Webring/ASTRI/Mechanical/front side of table.SLDPRT

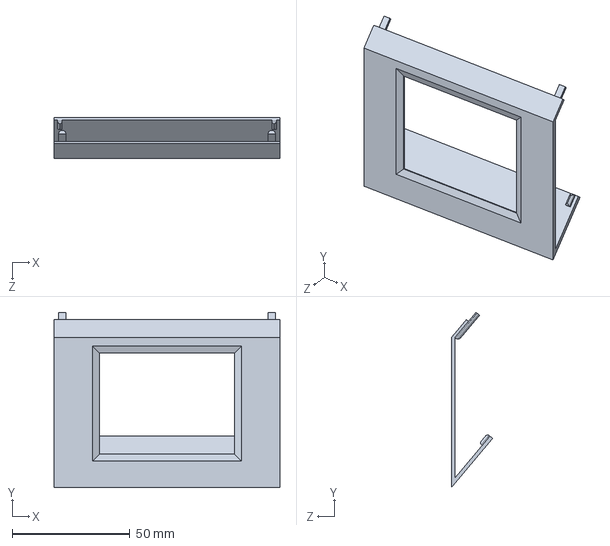
[picture p17: CAD file, 2019-09-15]
Mechanical/front side of table.SLDPRT
96.0 x 74.5 x 17.6 mm
