Webring/ASTRI/Mechanical/table bottom.SLDPRT

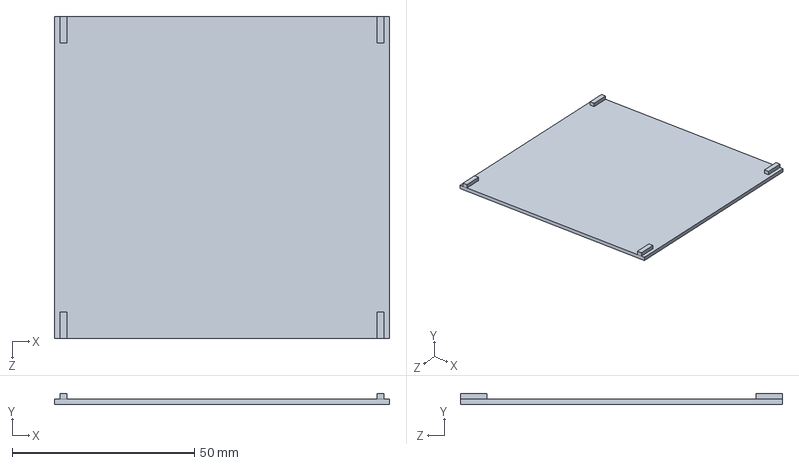
[picture p18: CAD file, 2019-09-15]
Mechanical/table bottom.SLDPRT
92.0 x 3.00 x 88.5 mm
