Webring/ASTRI/Mechanical/switch nozzle.SLDPRT

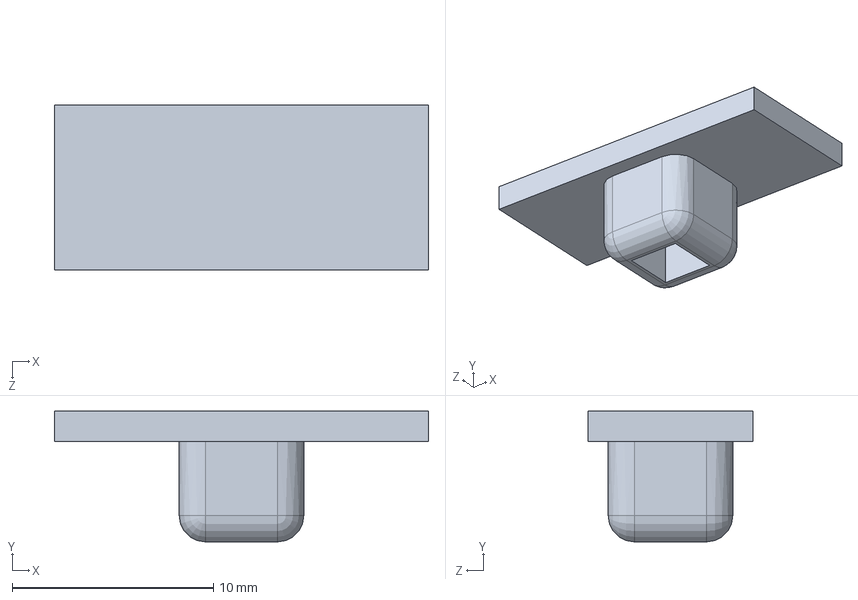
[picture p19: CAD file, 2019-09-15]
Mechanical/switch nozzle.SLDPRT
18.6 x 6.50 x 8.20 mm
