Webring/ASTRI/Mechanical/drum head.SLDPRT

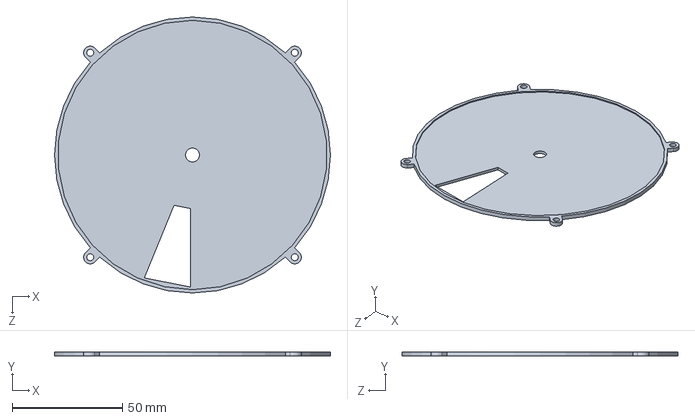
[picture p20: CAD file, 2019-08-11]
Mechanical/drum head.SLDPRT
125.0 x 2.00 x 125.0 mm
