Webring/ASTRI/Mechanical/drum body.SLDPRT

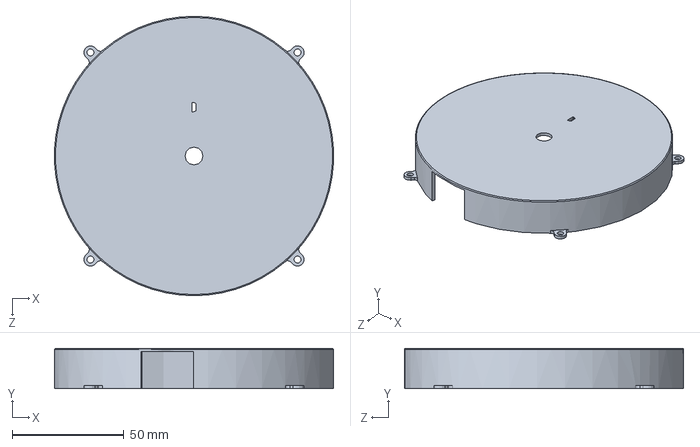
[picture p21: CAD file, 2019-08-11]
Mechanical/drum body.SLDPRT
124.8 x 18.0 x 125.0 mm
