Webring/ASTRI/Mechanical/motor mount to drum.SLDPRT

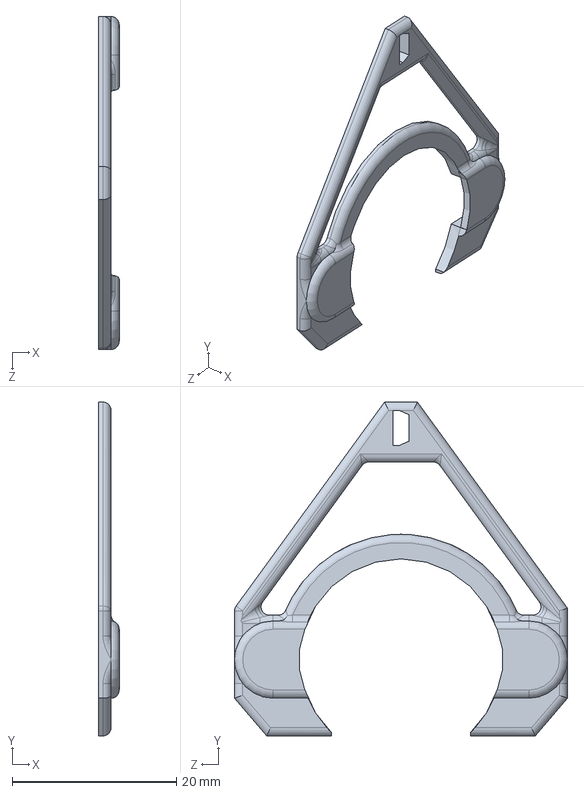
[picture p22: CAD file, 2019-08-11]
Mechanical/motor mount to drum.SLDPRT
2.50 x 40.6 x 40.5 mm
