Webring/ASTRI/Mechanical/drum.SLDPRT

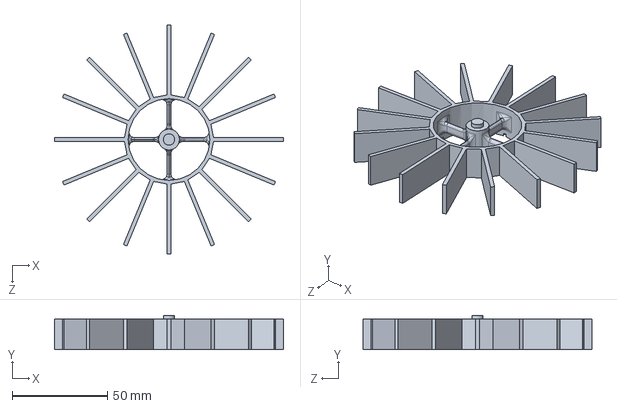
[picture p23: CAD file, 2019-08-11]
Mechanical/drum.SLDPRT
120.0 x 18.0 x 120.0 mm
